sabotrax/monisrahmen/site_documents/pictures/frame2_back.jpg

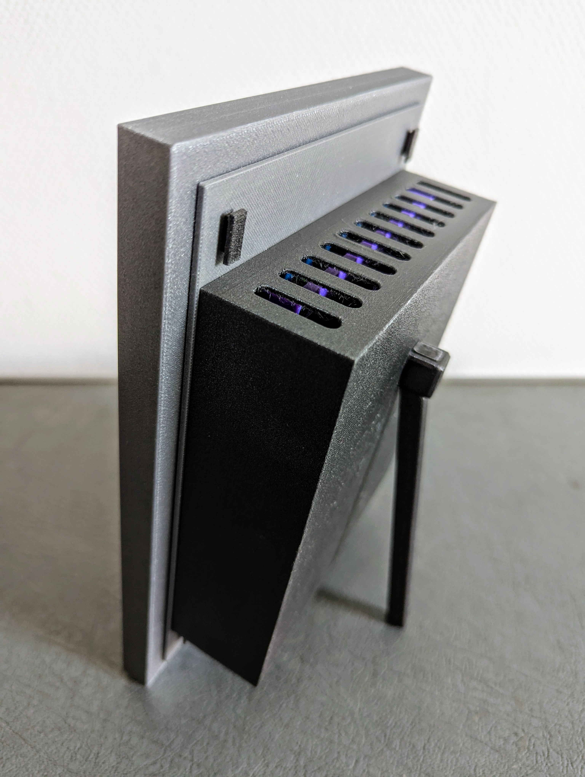
site_documents/pictures/frame2_back.jpg
