sabotrax/monisrahmen/site_documents/pictures/frame2_board.jpg

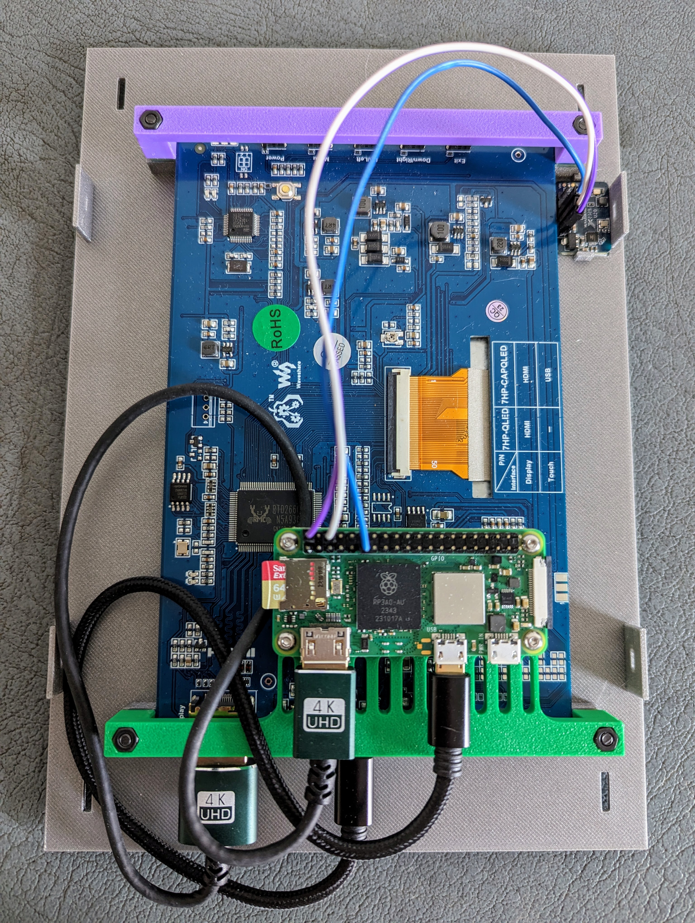
site_documents/pictures/frame2_board.jpg
